8Bit-P/R.O.B.E.R.T/HardwareAndDesigns/Case/Arduino Mega 2560 _ RAMPS Holder with Quick Release - 2165053/images/20170305_114258__.jpg

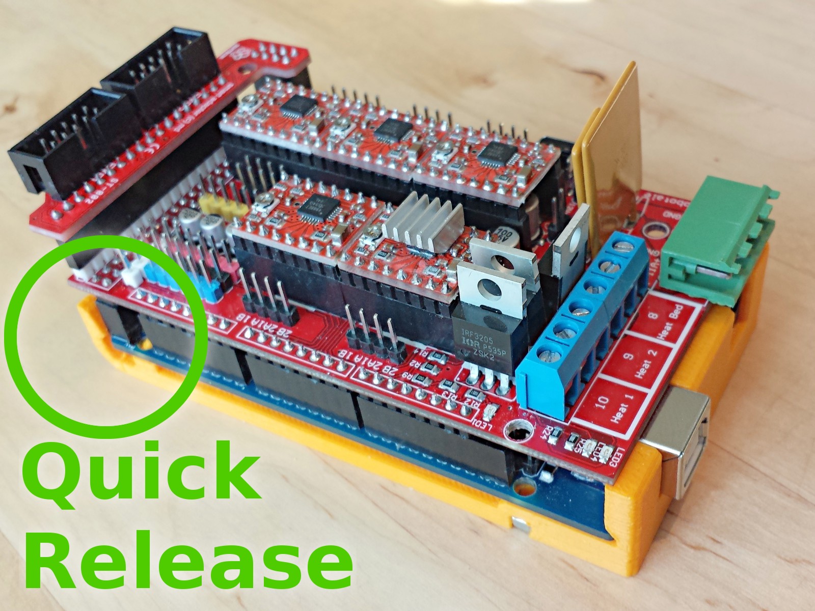
HardwareAndDesigns/Case/Arduino Mega 2560 _ RAMPS Holder with Quick Release - 2165053/images/20170305_114258__.jpg
