8Bit-P/R.O.B.E.R.T/HardwareAndDesigns/Robot Solidworks model/v.5/Motor 5 adapter.SLDPRT

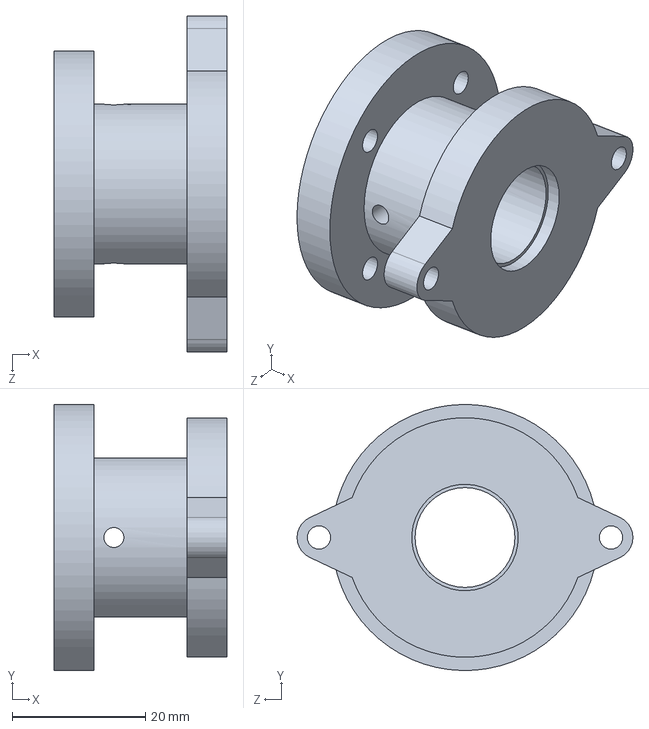
[picture p21: CAD file, 2024-06-12]
HardwareAndDesigns/Robot Solidworks model/v.5/Motor 5 adapter.SLDPRT
26.0 x 40.0 x 50.5 mm
