8Bit-P/R.O.B.E.R.T/HardwareAndDesigns/Stand/Baseplate.STL

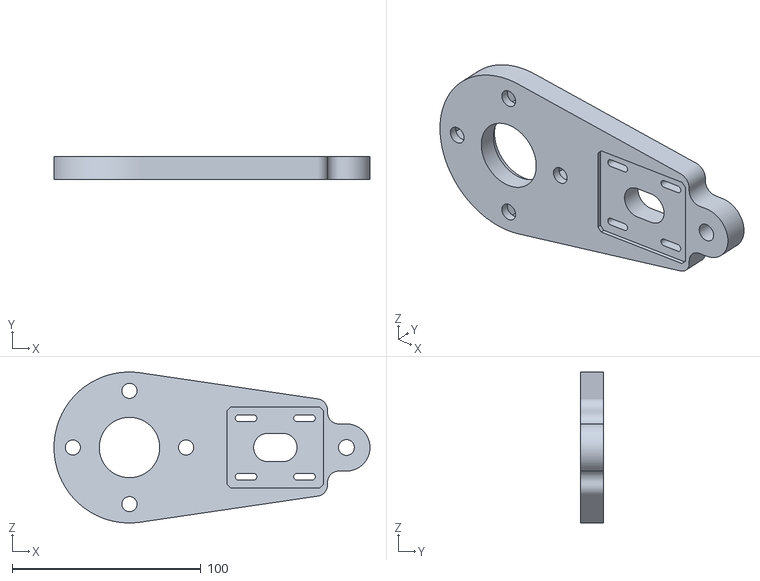
[picture p22: CAD file, 2024-06-12]
HardwareAndDesigns/Stand/Baseplate.STL
167.5 x 12.0 x 80.0
