8Bit-P/R.O.B.E.R.T/HardwareAndDesigns/Additional/LimitSwitchBase.stl

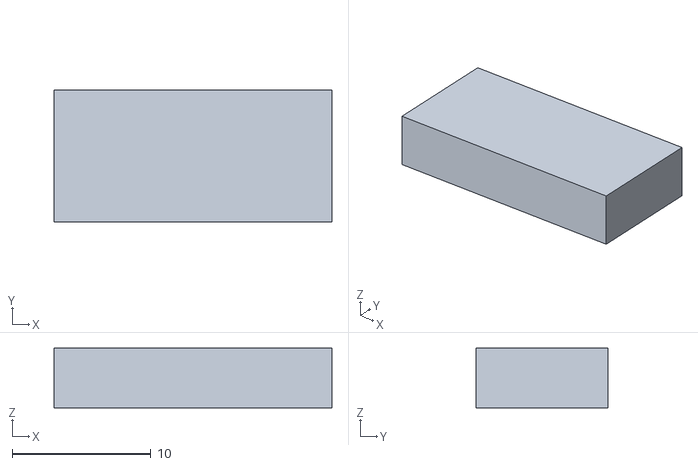
[picture p23: CAD file, 2024-12-18]
HardwareAndDesigns/Additional/LimitSwitchBase.stl
20.0 x 9.50 x 4.30
