8Bit-P/R.O.B.E.R.T/HardwareAndDesigns/Arm2/Rotation arm V3.STL

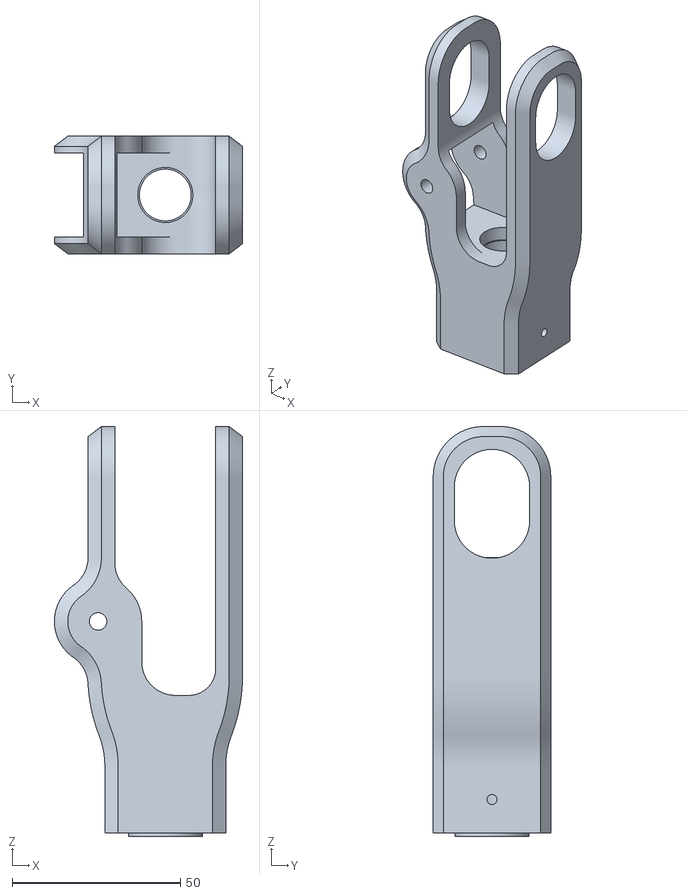
[picture p24: CAD file, 2024-06-12]
HardwareAndDesigns/Arm2/Rotation arm V3.STL
56.0 x 35.0 x 122.0
