8Bit-P/R.O.B.E.R.T/HardwareAndDesigns/Base/BaseWall_2_v2.STL

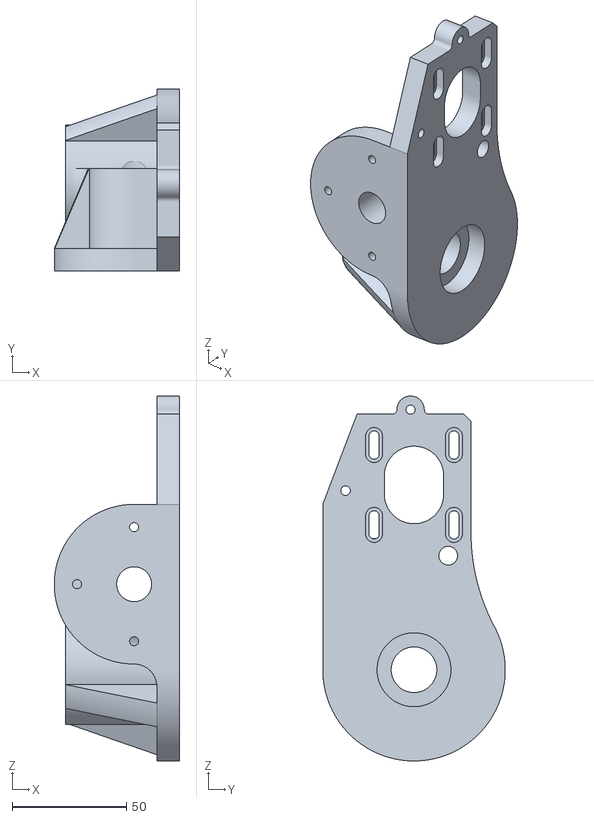
[picture p25: CAD file, 2024-06-12]
HardwareAndDesigns/Base/BaseWall_2_v2.STL
55.0 x 80.0 x 160.0
