8Bit-P/R.O.B.E.R.T/HardwareAndDesigns/Case/PowerSupplySupport.stl

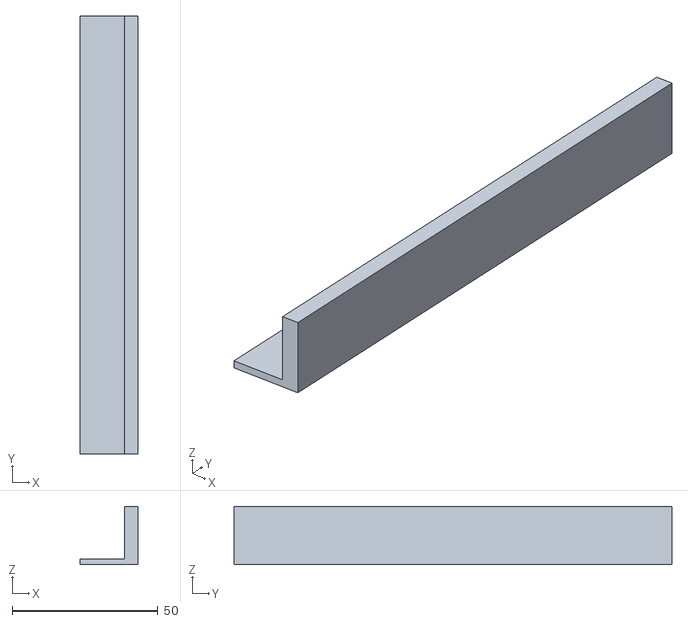
[picture p26: CAD file, 2025-02-12]
HardwareAndDesigns/Case/PowerSupplySupport.stl
20.0 x 150.0 x 20.0
