8Bit-P/R.O.B.E.R.T/HardwareAndDesigns/PiecesRework/ReductorSeparator.stl

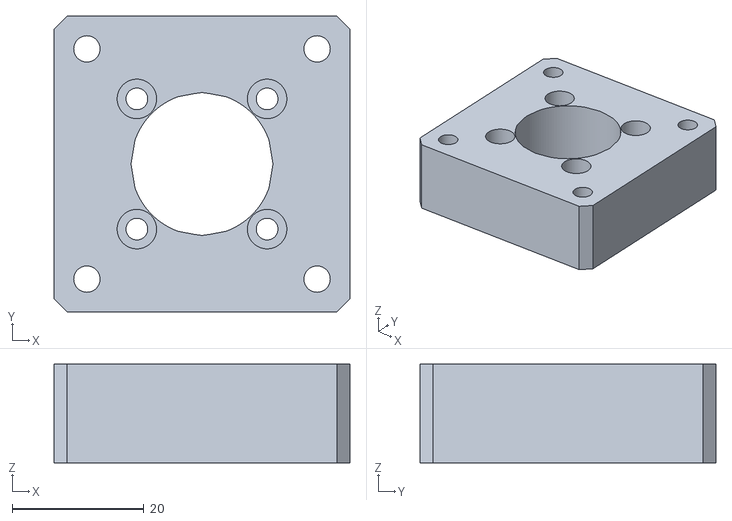
[picture p27: CAD file, 2024-12-13]
HardwareAndDesigns/PiecesRework/ReductorSeparator.stl
45.0 x 45.0 x 15.0
