8Bit-P/R.O.B.E.R.T/HardwareAndDesigns/Robot Solidworks model/Arm 4.3.SLDPRT

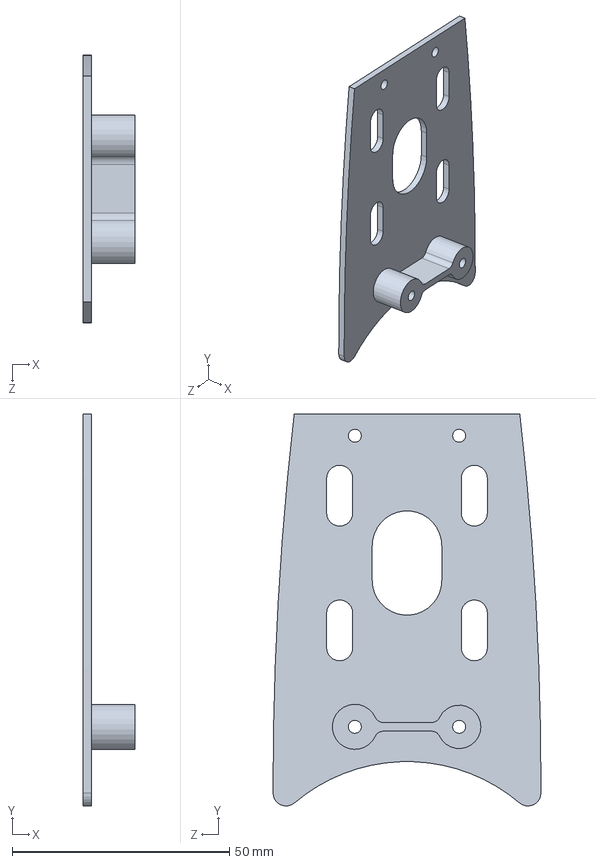
[picture p28: CAD file, 2024-06-12]
HardwareAndDesigns/Robot Solidworks model/Arm 4.3.SLDPRT
12.0 x 90.2 x 61.7 mm
