8Bit-P/R.O.B.E.R.T/HardwareAndDesigns/Robot Solidworks model/microswitch-ss-3gl13sl-1.snapshot.2/switch_lever.SLDPRT

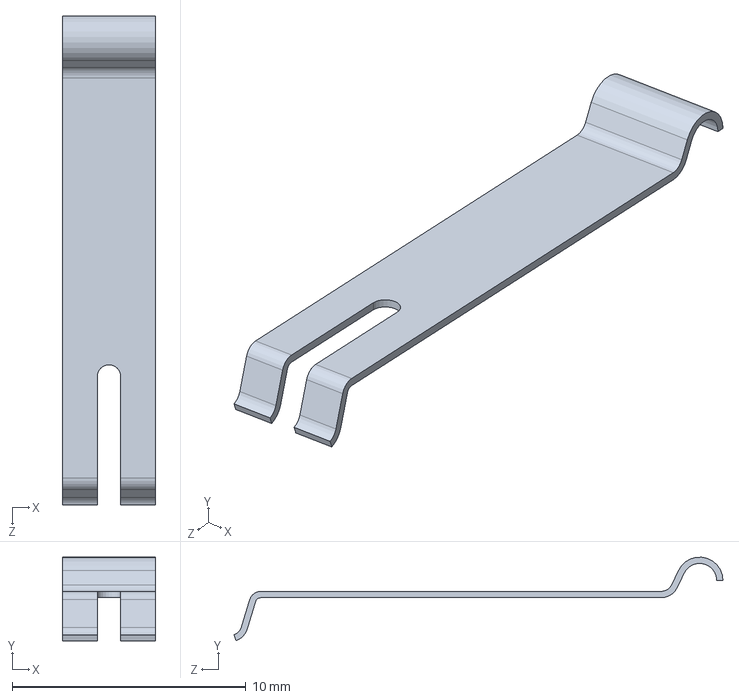
[picture p29: CAD file, 2024-06-12]
HardwareAndDesigns/Robot Solidworks model/microswitch-ss-3gl13sl-1.snapshot.2/switch_lever.SLDPRT
4.00 x 3.58 x 20.9 mm
