8Bit-P/R.O.B.E.R.T/HardwareAndDesigns/Robot Solidworks model/Solidworks/Nema 14 stepper.SLDPRT

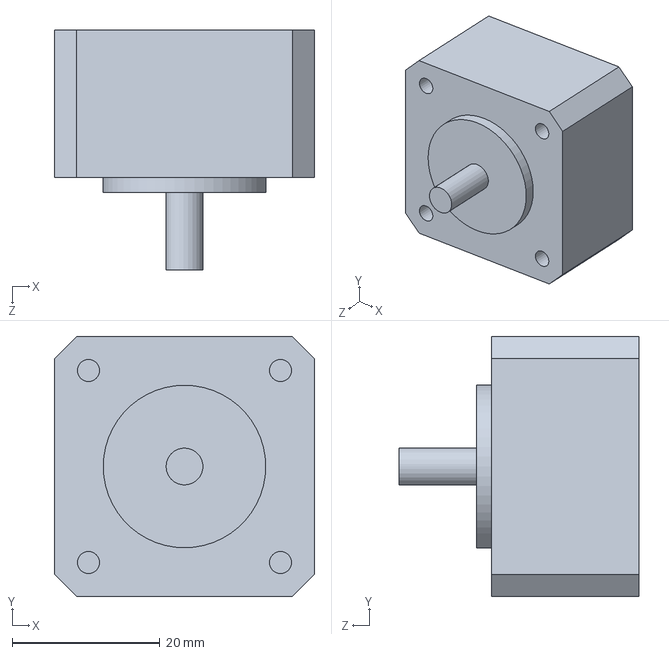
[picture p30: CAD file, 2024-06-12]
HardwareAndDesigns/Robot Solidworks model/Solidworks/Nema 14 stepper.SLDPRT
35.2 x 35.2 x 32.5 mm
