8Bit-P/R.O.B.E.R.T/HardwareAndDesigns/Robot Solidworks model/v.5/Pulley60Tv2.SLDPRT

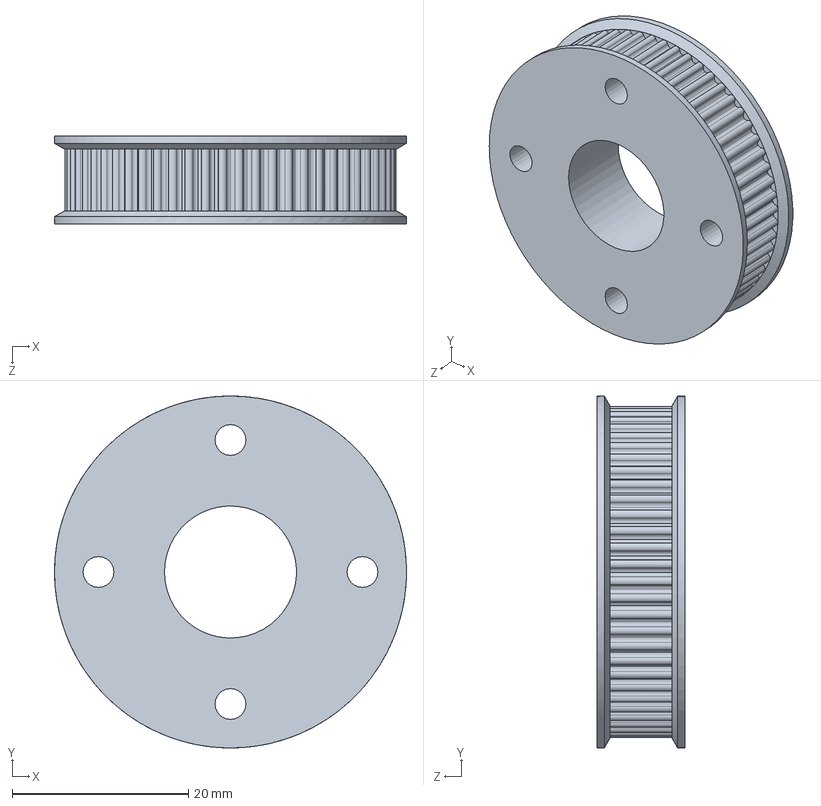
[picture p32: CAD file, 2024-06-12]
HardwareAndDesigns/Robot Solidworks model/v.5/Pulley60Tv2.SLDPRT
40.0 x 40.0 x 10.0 mm
