8Bit-P/R.O.B.E.R.T/HardwareAndDesigns/Stand/Bottom Tube.STL

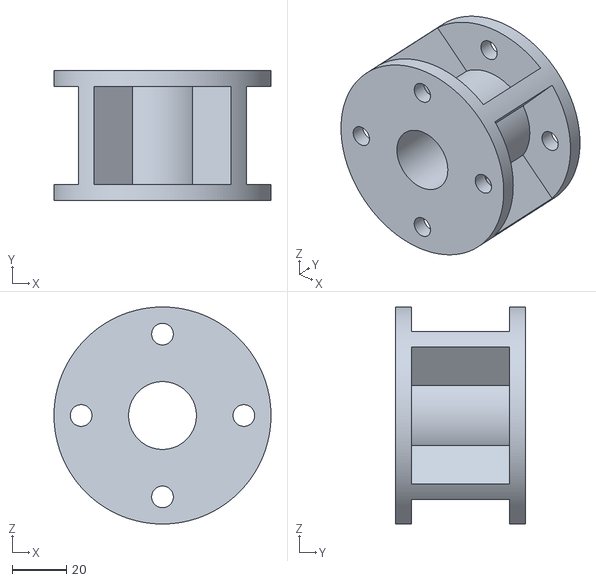
[picture p33: CAD file, 2024-06-12]
HardwareAndDesigns/Stand/Bottom Tube.STL
80.0 x 48.0 x 80.0
