8Bit-P/R.O.B.E.R.T/HardwareAndDesigns/Arm1/Arm1v2.STL

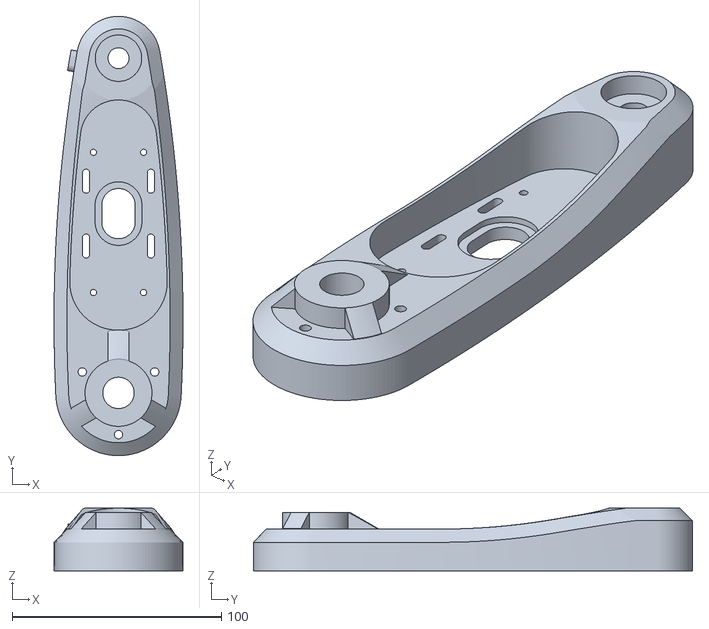
[picture p34: CAD file, 2024-06-12]
HardwareAndDesigns/Arm1/Arm1v2.STL
61.7 x 210.0 x 30.0
