8Bit-P/R.O.B.E.R.T/HardwareAndDesigns/Arm2/Pulley32TGT2.STL

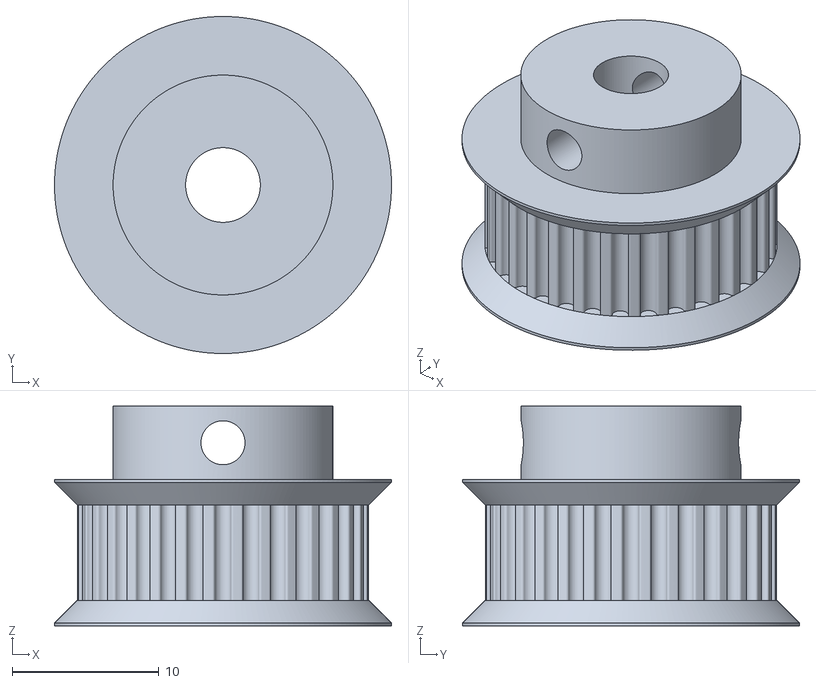
[picture p35: CAD file, 2024-06-12]
HardwareAndDesigns/Arm2/Pulley32TGT2.STL
23.0 x 23.0 x 15.0
