8Bit-P/R.O.B.E.R.T/HardwareAndDesigns/Base/Motor1 spacer.STL

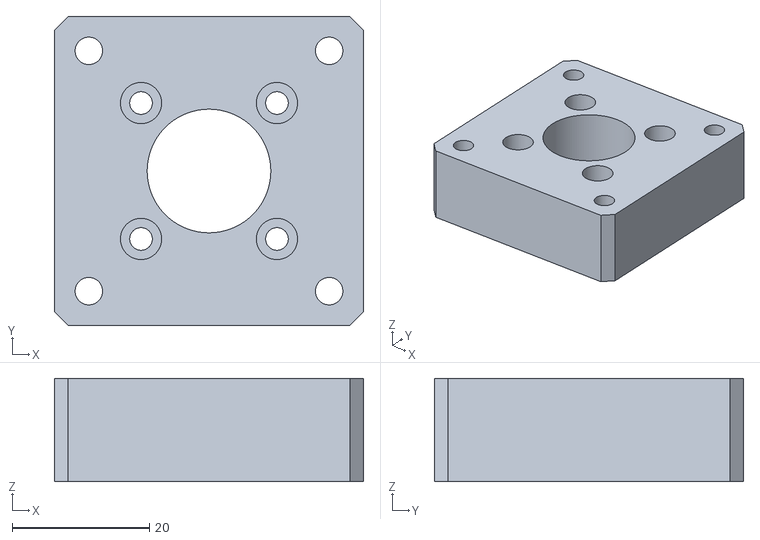
[picture p36: CAD file, 2024-06-12]
HardwareAndDesigns/Base/Motor1 spacer.STL
45.0 x 45.0 x 15.0
