8Bit-P/R.O.B.E.R.T/HardwareAndDesigns/Case/PowerSupplyHolder.stl

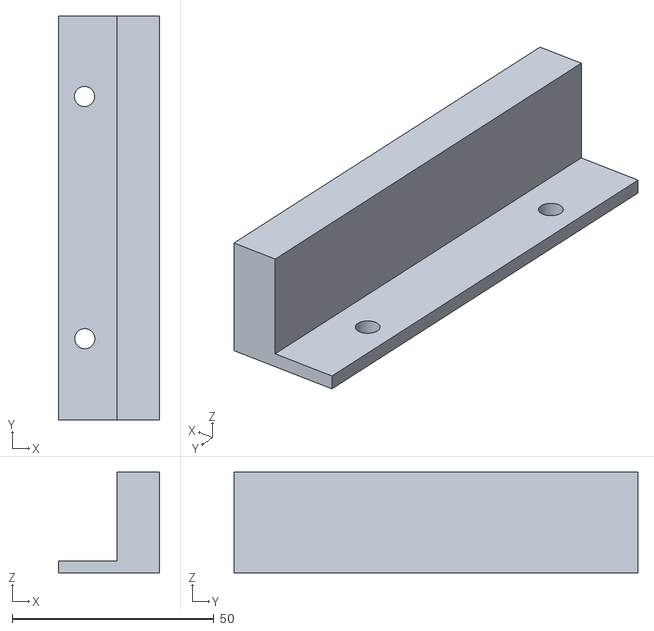
[picture p37: CAD file, 2025-02-12]
HardwareAndDesigns/Case/PowerSupplyHolder.stl
25.0 x 100.0 x 25.0
