8Bit-P/R.O.B.E.R.T/HardwareAndDesigns/Robot Solidworks model/ball bearings/thrust ball bearing_68_iso.sldprt

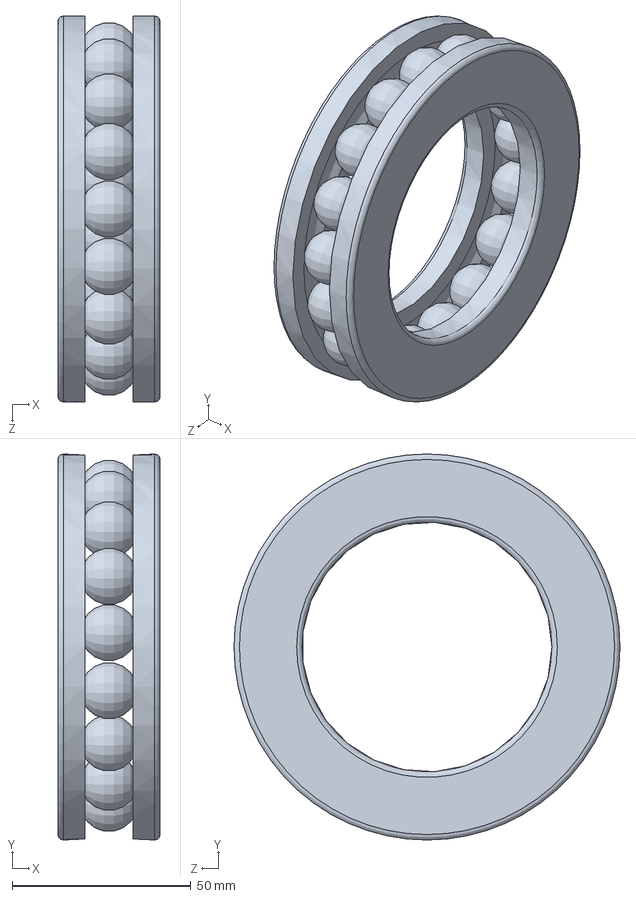
[picture p38: CAD file, 2024-06-12]
HardwareAndDesigns/Robot Solidworks model/ball bearings/thrust ball bearing_68_iso.sldprt
28.6 x 108.0 x 108.0 mm
