8Bit-P/R.O.B.E.R.T/HardwareAndDesigns/Robot Solidworks model/Solidworks/GT2_16T_13x14.SLDPRT

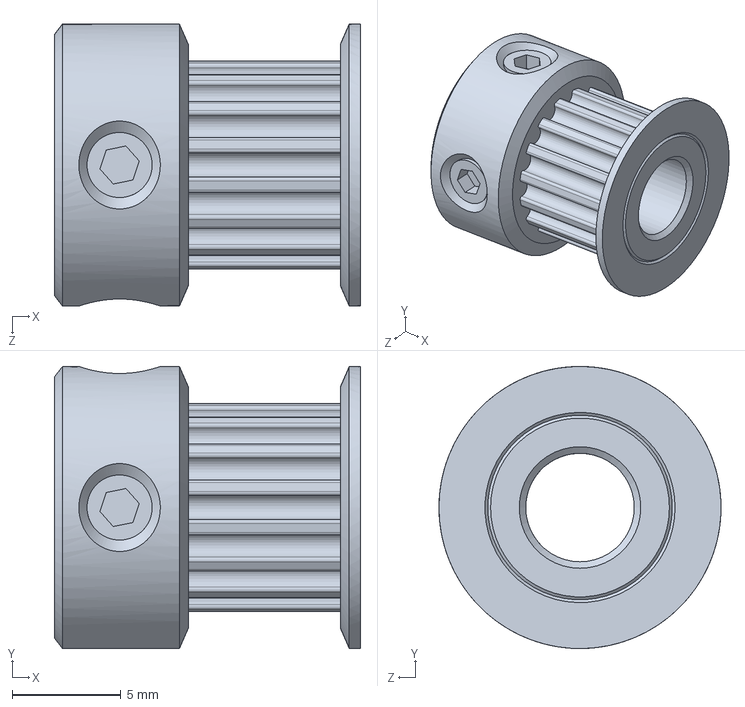
[picture p39: CAD file, 2024-06-12]
HardwareAndDesigns/Robot Solidworks model/Solidworks/GT2_16T_13x14.SLDPRT
14.1 x 13.0 x 13.0 mm
