8Bit-P/R.O.B.E.R.T/HardwareAndDesigns/Stand/Bottom support.STL

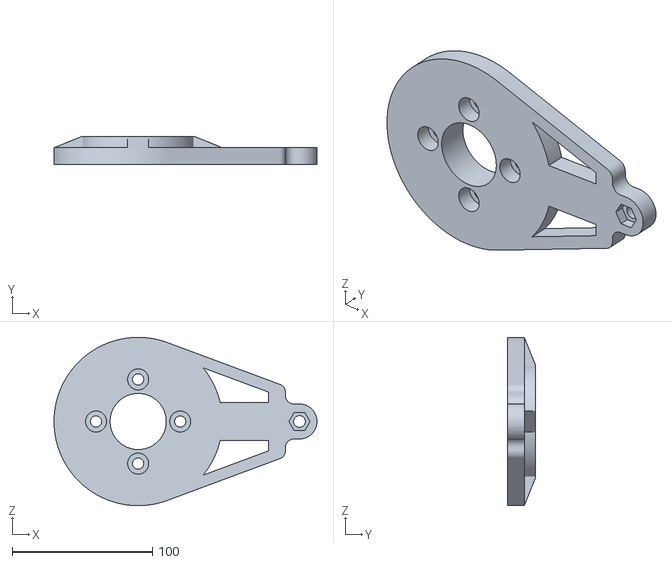
[picture p40: CAD file, 2024-06-12]
HardwareAndDesigns/Stand/Bottom support.STL
187.5 x 20.0 x 120.0
