8Bit-P/R.O.B.E.R.T/HardwareAndDesigns/Arm1/HTD80T 2mm spacer.STL

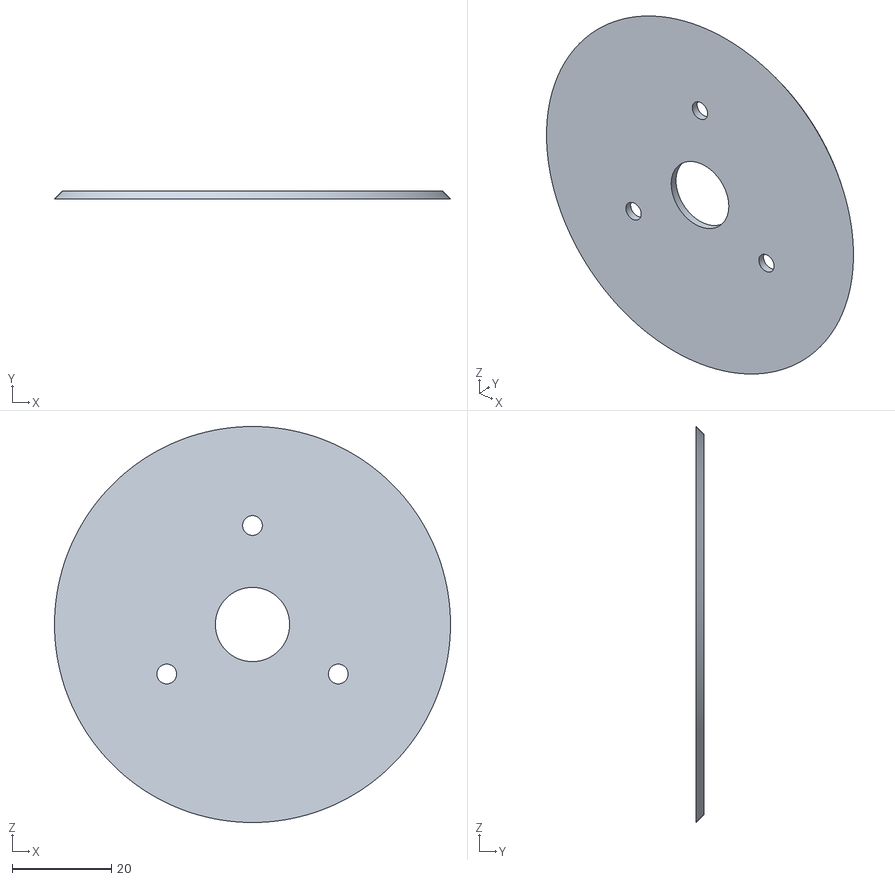
[picture p41: CAD file, 2024-06-12]
HardwareAndDesigns/Arm1/HTD80T 2mm spacer.STL
80.0 x 1.60 x 80.0
