8Bit-P/R.O.B.E.R.T/HardwareAndDesigns/Arm2/Arm2Mountv2.STL

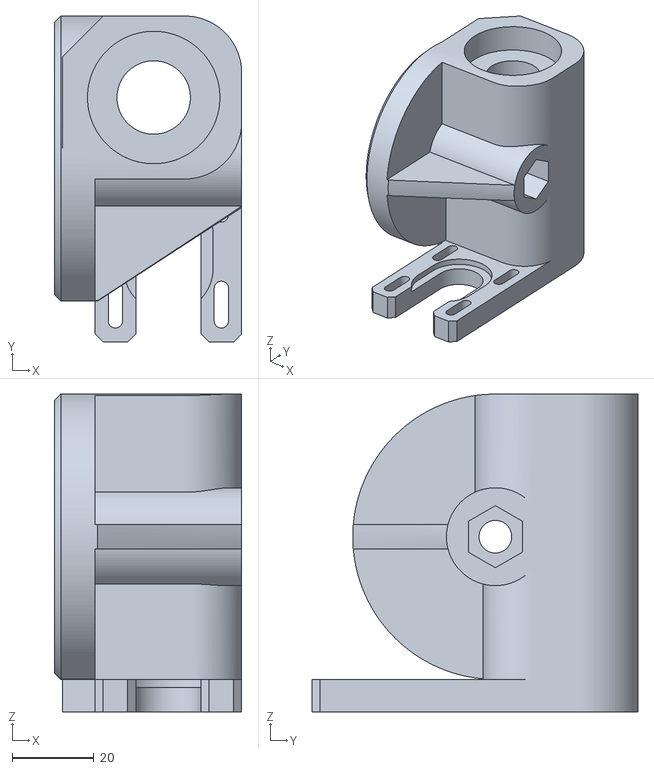
[picture p42: CAD file, 2024-06-12]
HardwareAndDesigns/Arm2/Arm2Mountv2.STL
46.0 x 80.0 x 78.0
