8Bit-P/R.O.B.E.R.T/HardwareAndDesigns/Base/Basewall cover v2.STL

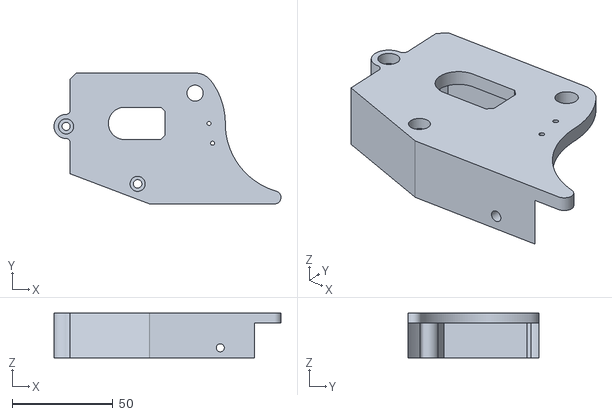
[picture p43: CAD file, 2024-06-12]
HardwareAndDesigns/Base/Basewall cover v2.STL
112.6 x 65.0 x 22.2
