8Bit-P/R.O.B.E.R.T/HardwareAndDesigns/Case/BottomPlate2.stl

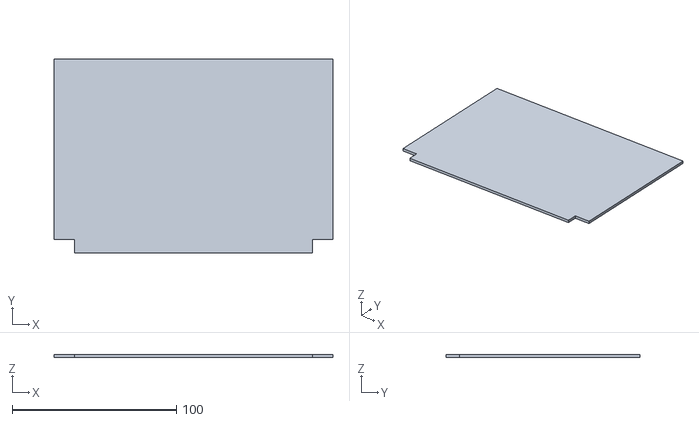
[picture p44: CAD file, 2025-02-12]
HardwareAndDesigns/Case/BottomPlate2.stl
170.0 x 118.0 x 2.00
