8Bit-P/R.O.B.E.R.T/HardwareAndDesigns/Robot Solidworks model/microswitch-ss-3gl13sl-1.snapshot.2/limit-switch-top-case.SLDPRT

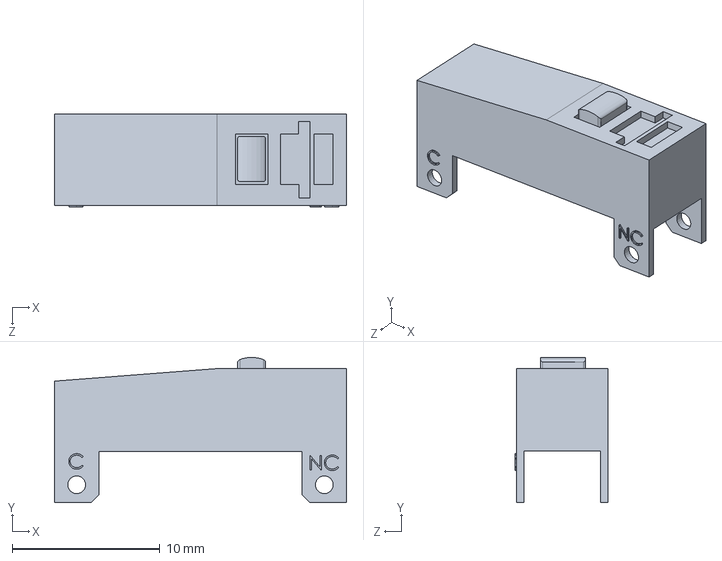
[picture p45: CAD file, 2024-06-12]
HardwareAndDesigns/Robot Solidworks model/microswitch-ss-3gl13sl-1.snapshot.2/limit-switch-top-case.SLDPRT
19.8 x 9.81 x 6.30 mm
