8Bit-P/R.O.B.E.R.T/HardwareAndDesigns/Robot Solidworks model/Solidworks/Nema 14 Round stepper.SLDPRT

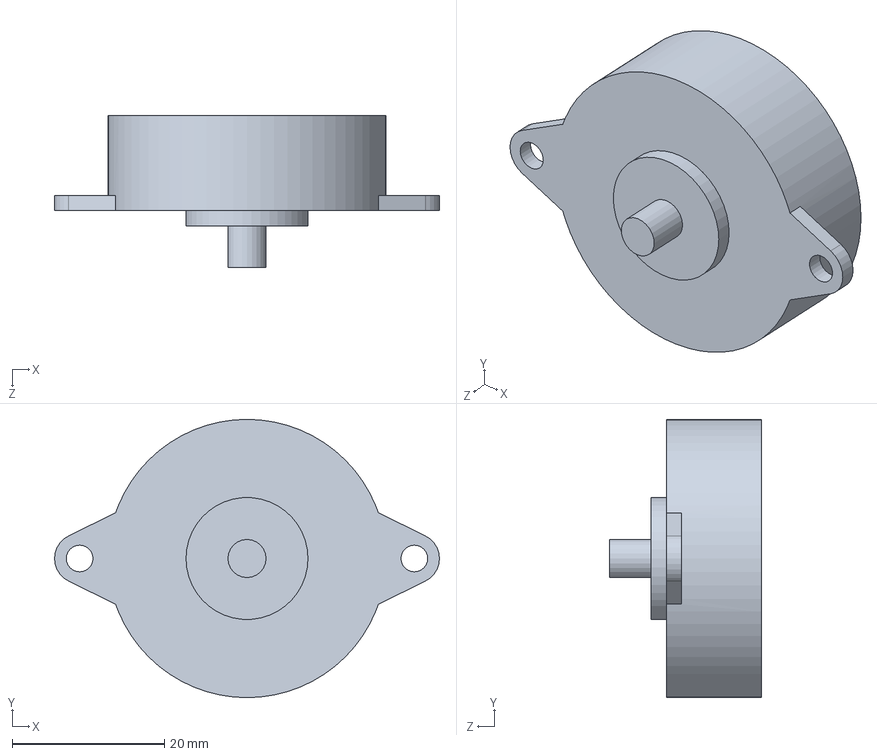
[picture p46: CAD file, 2024-06-12]
HardwareAndDesigns/Robot Solidworks model/Solidworks/Nema 14 Round stepper.SLDPRT
50.5 x 36.5 x 20.0 mm
