8Bit-P/R.O.B.E.R.T/HardwareAndDesigns/Robot Solidworks model/stepper-motor-nema-17.snapshot.17/Base.SLDPRT

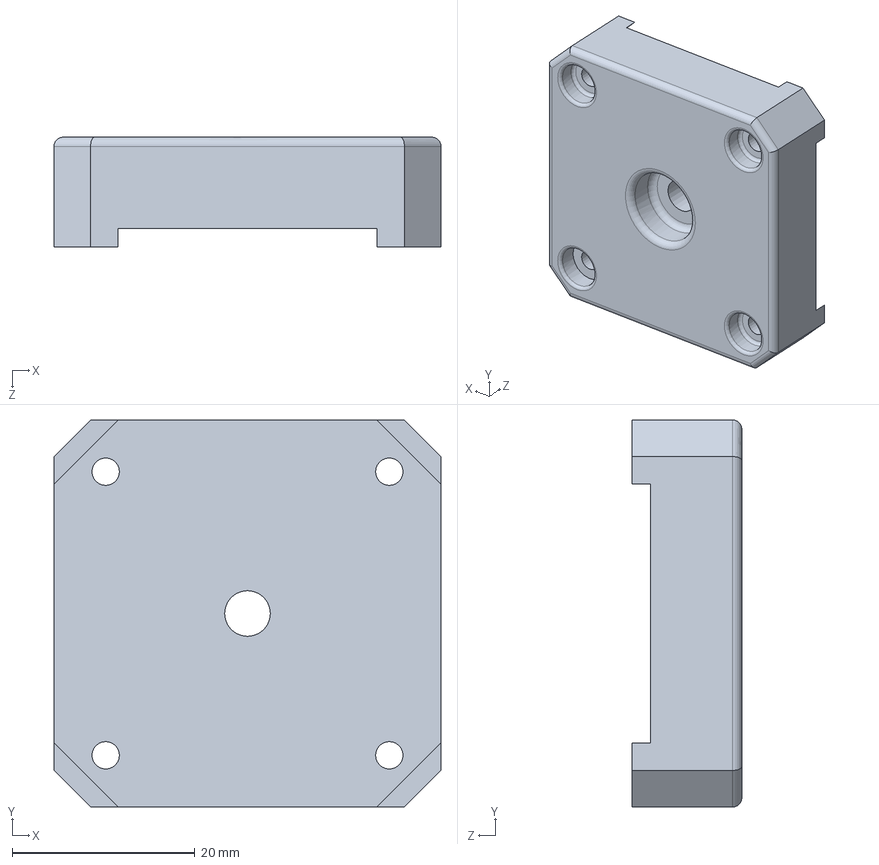
[picture p47: CAD file, 2024-06-12]
HardwareAndDesigns/Robot Solidworks model/stepper-motor-nema-17.snapshot.17/Base.SLDPRT
42.3 x 42.3 x 12.0 mm
