8Bit-P/R.O.B.E.R.T/HardwareAndDesigns/Case/Base Top Half.stl

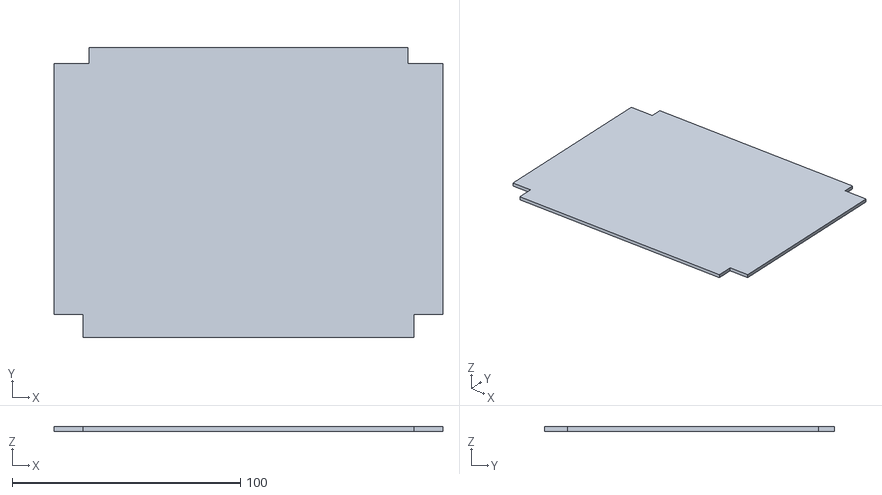
[picture p48: CAD file, 2025-02-12]
HardwareAndDesigns/Case/Base Top Half.stl
170.5 x 127.0 x 2.00
