8Bit-P/R.O.B.E.R.T/HardwareAndDesigns/Robot Solidworks model/microswitch-ss-3gl13sl-1.snapshot.2/pins.SLDPRT

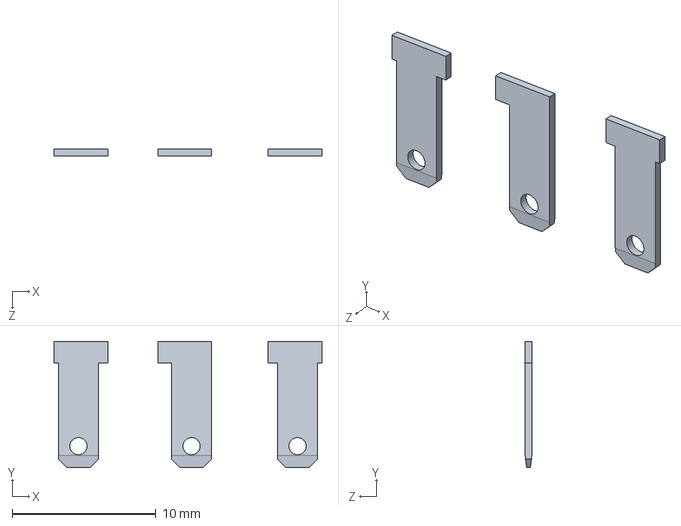
[picture p49: CAD file, 2024-06-12]
HardwareAndDesigns/Robot Solidworks model/microswitch-ss-3gl13sl-1.snapshot.2/pins.SLDPRT
18.6 x 8.80 x 0.47 mm
