8Bit-P/R.O.B.E.R.T/HardwareAndDesigns/Robot Solidworks model/stepper-motor-nema-17.snapshot.17/Eje.SLDPRT

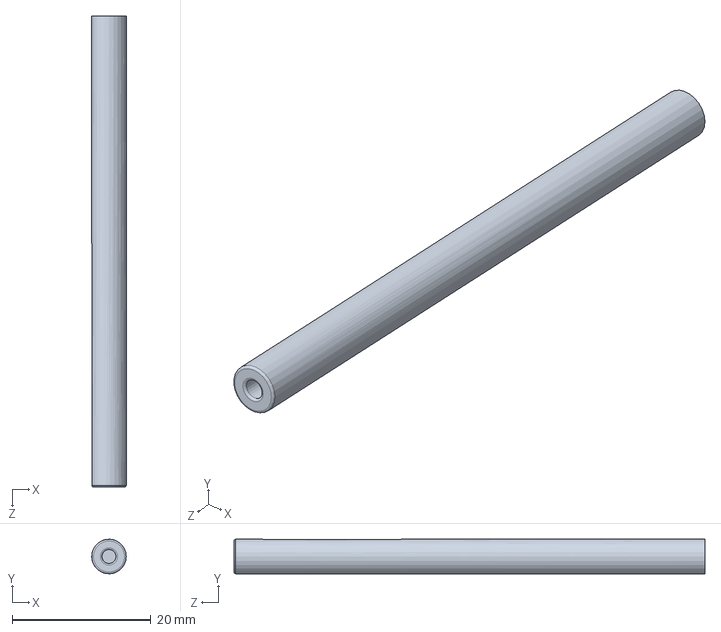
[picture p50: CAD file, 2024-06-12]
HardwareAndDesigns/Robot Solidworks model/stepper-motor-nema-17.snapshot.17/Eje.SLDPRT
5.00 x 5.00 x 68.0 mm
