8Bit-P/R.O.B.E.R.T/HardwareAndDesigns/Case/ConnectorPannel v5.stl

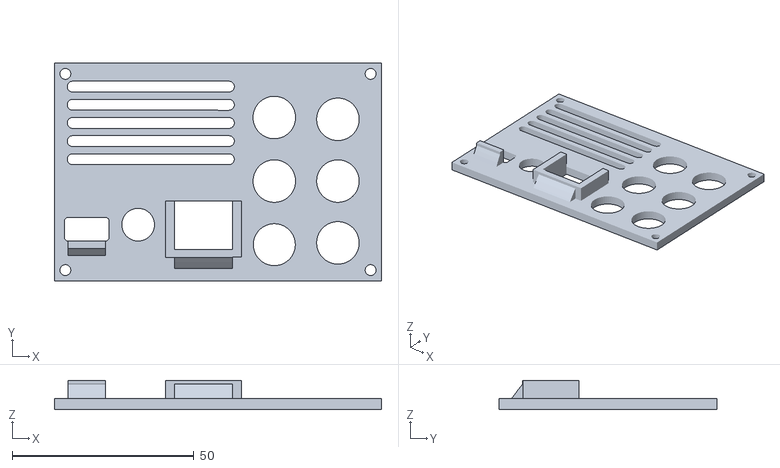
[picture p51: CAD file, 2025-02-12]
HardwareAndDesigns/Case/ConnectorPannel v5.stl
90.0 x 60.0 x 8.00
