8Bit-P/R.O.B.E.R.T/HardwareAndDesigns/Robot Solidworks model/3M HTD 16T 6mm Bore.SLDPRT

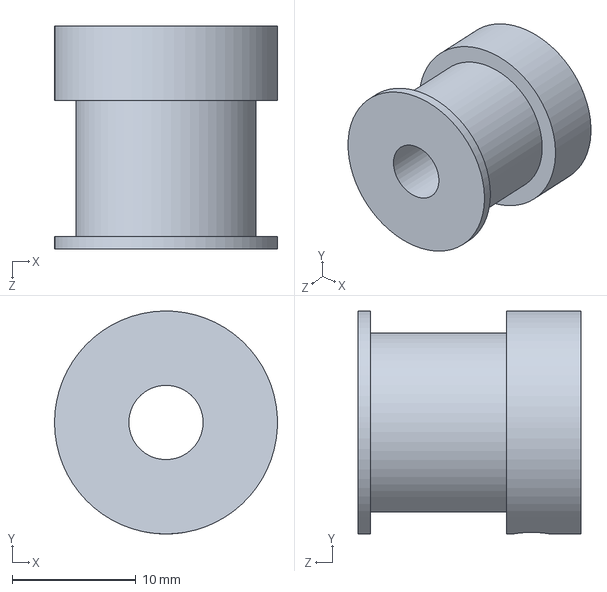
[picture p52: CAD file, 2024-06-12]
HardwareAndDesigns/Robot Solidworks model/3M HTD 16T 6mm Bore.SLDPRT
18.0 x 18.0 x 18.0 mm
