8Bit-P/R.O.B.E.R.T/HardwareAndDesigns/Arm2/GT2 belt chamfer roller.STL

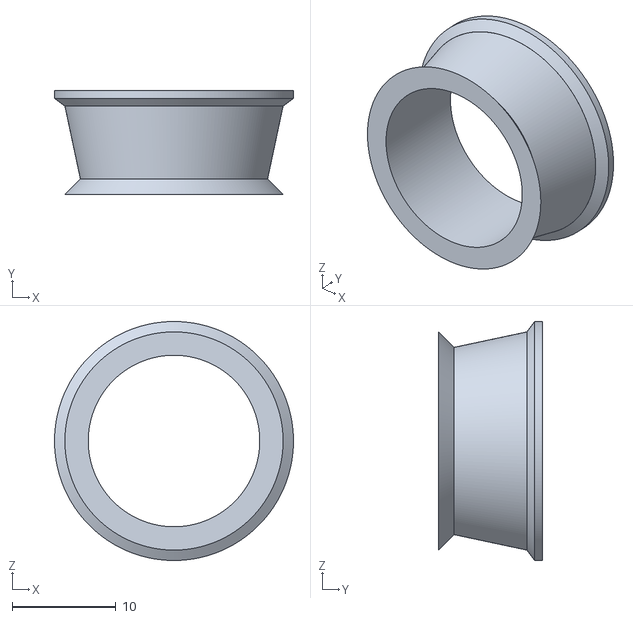
[picture p53: CAD file, 2024-06-12]
HardwareAndDesigns/Arm2/GT2 belt chamfer roller.STL
23.0 x 10.0 x 23.0
