8Bit-P/R.O.B.E.R.T/HardwareAndDesigns/Case/USBc v1.stl

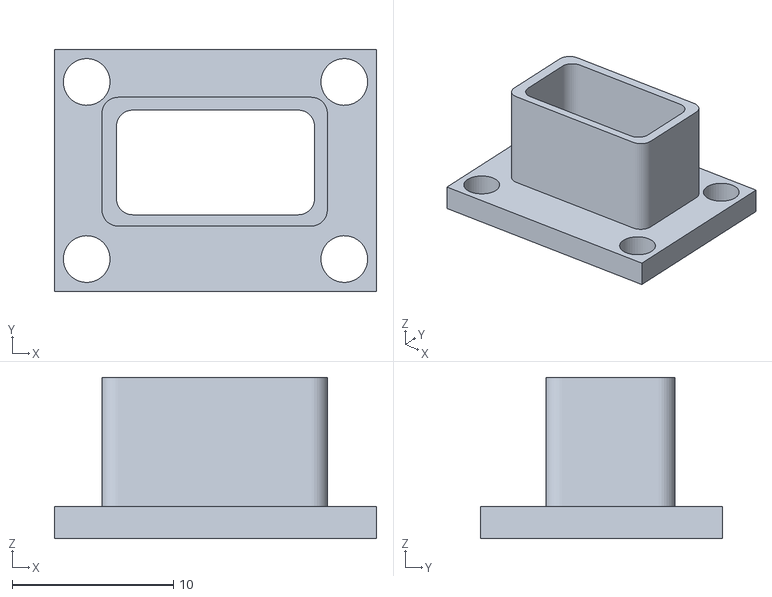
[picture p54: CAD file, 2025-02-12]
HardwareAndDesigns/Case/USBc v1.stl
20.0 x 15.0 x 10.0
