8Bit-P/R.O.B.E.R.T/HardwareAndDesigns/Robot Solidworks model/Pulley100Tv5.SLDPRT

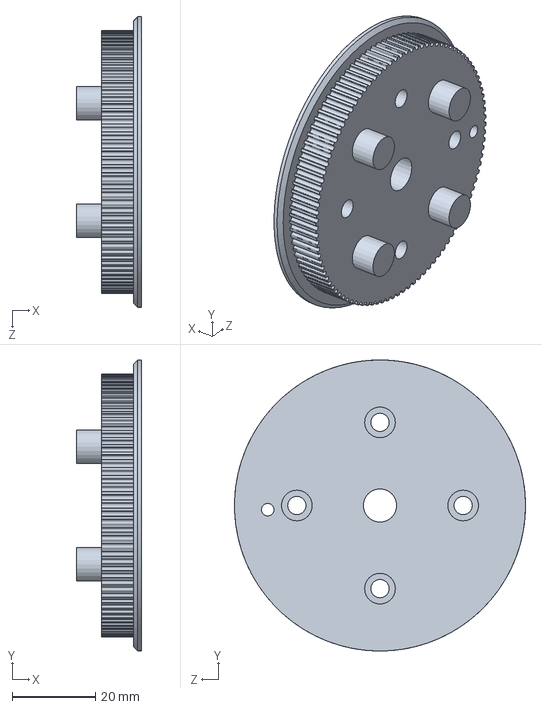
[picture p55: CAD file, 2024-06-12]
HardwareAndDesigns/Robot Solidworks model/Pulley100Tv5.SLDPRT
15.6 x 70.0 x 70.0 mm
