8Bit-P/R.O.B.E.R.T/HardwareAndDesigns/Arm2/J6 housing.STL

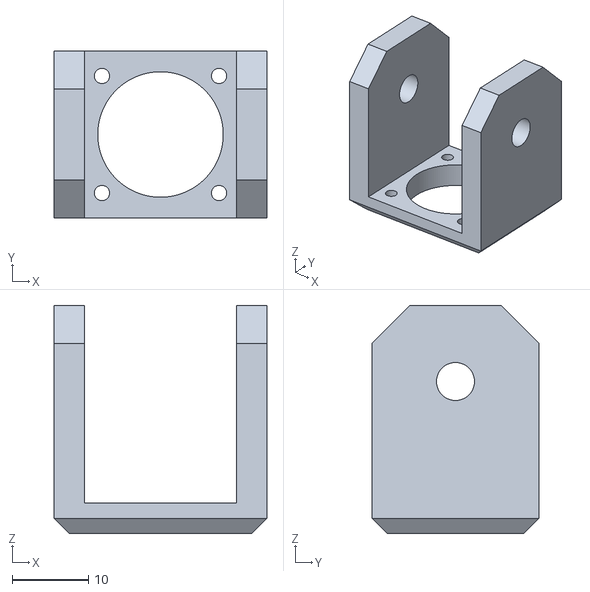
[picture p56: CAD file, 2024-06-12]
HardwareAndDesigns/Arm2/J6 housing.STL
28.0 x 22.0 x 30.0
