8Bit-P/R.O.B.E.R.T/HardwareAndDesigns/Case/ConnectorPannel.stl

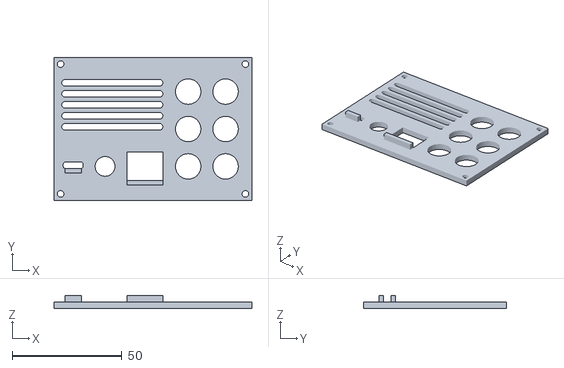
[picture p57: CAD file, 2025-02-12]
HardwareAndDesigns/Case/ConnectorPannel.stl
90.0 x 65.0 x 6.00
