8Bit-P/R.O.B.E.R.T/HardwareAndDesigns/Case/Box.stl

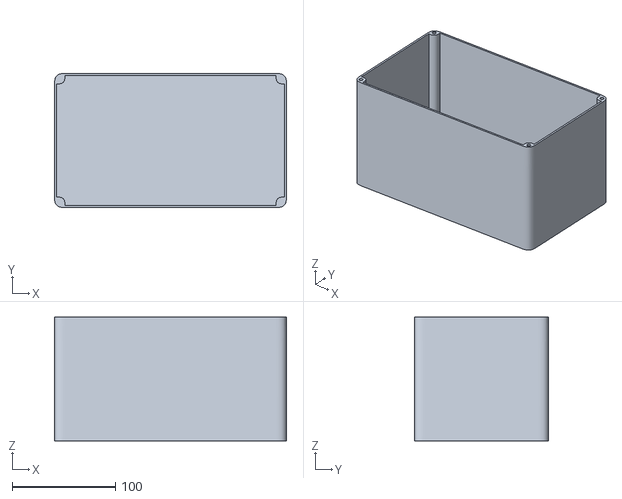
[picture p58: CAD file, 2024-12-18]
HardwareAndDesigns/Case/Box.stl
225.0 x 130.0 x 120.0
