8Bit-P/R.O.B.E.R.T/HardwareAndDesigns/Case/Electronics Box 180mmx130mmx60mm.SLDPRT

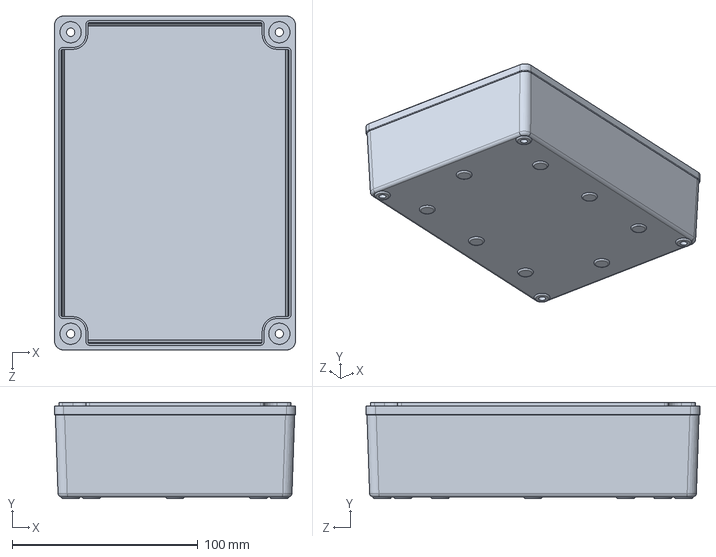
[picture p59: CAD file, 2024-12-13]
HardwareAndDesigns/Case/Electronics Box 180mmx130mmx60mm.SLDPRT
130.0 x 52.0 x 180.0 mm
