8Bit-P/R.O.B.E.R.T/HardwareAndDesigns/Robot Solidworks model/100mm aluputki.SLDPRT

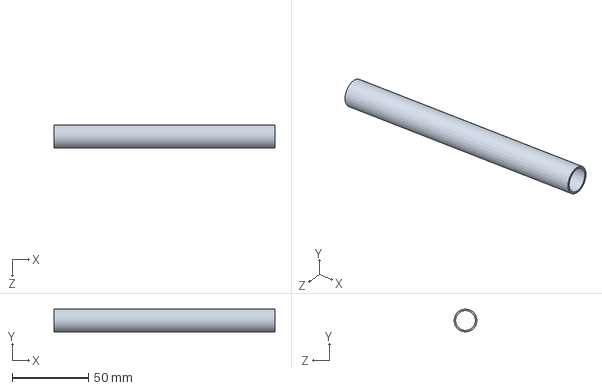
[picture p60: CAD file, 2024-06-12]
HardwareAndDesigns/Robot Solidworks model/100mm aluputki.SLDPRT
145.0 x 15.0 x 15.0 mm
