8Bit-P/R.O.B.E.R.T/HardwareAndDesigns/Robot Solidworks model/6mm akseli.SLDPRT

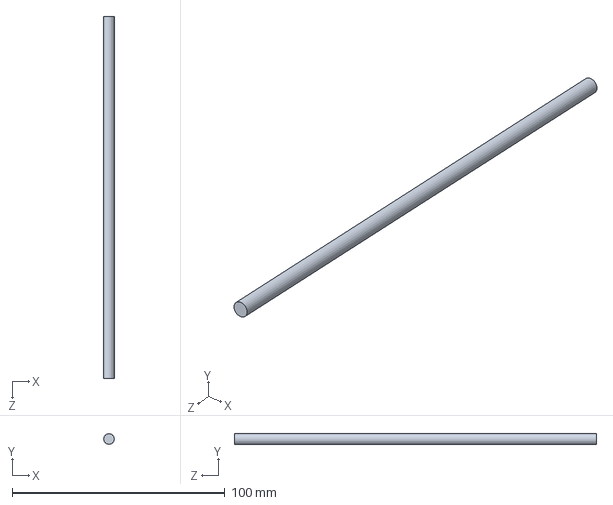
[picture p61: CAD file, 2024-06-12]
HardwareAndDesigns/Robot Solidworks model/6mm akseli.SLDPRT
5.00 x 5.00 x 170.0 mm
