8Bit-P/R.O.B.E.R.T/HardwareAndDesigns/Robot Solidworks model/Nema8 Stepperi (banggood.com).SLDPRT

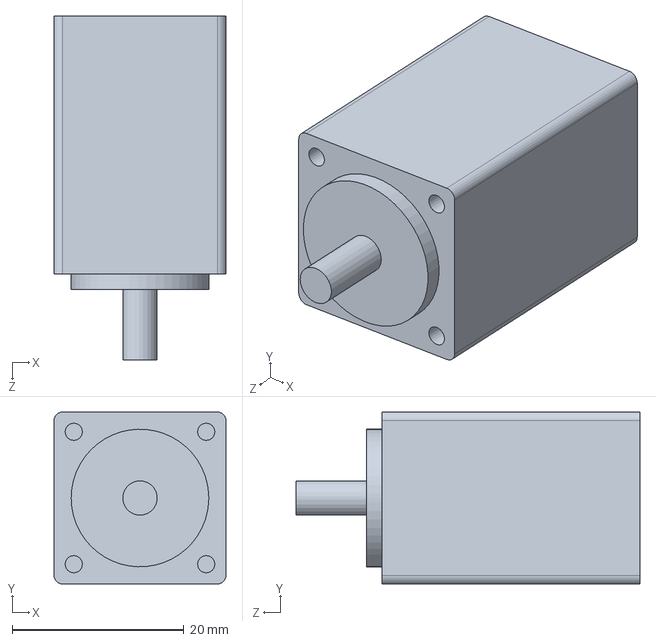
[picture p62: CAD file, 2024-06-12]
HardwareAndDesigns/Robot Solidworks model/Nema8 Stepperi (banggood.com).SLDPRT
20.0 x 20.0 x 40.0 mm
