8Bit-P/R.O.B.E.R.T/HardwareAndDesigns/Robot Solidworks model/Nema 17 planetary 5 to 1 gearbox.SLDPRT

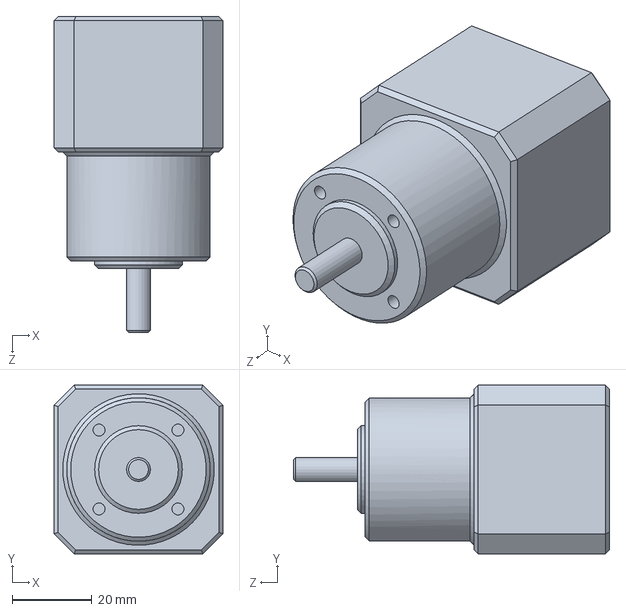
[picture p63: CAD file, 2024-06-12]
HardwareAndDesigns/Robot Solidworks model/Nema 17 planetary 5 to 1 gearbox.SLDPRT
42.3 x 42.3 x 79.3 mm
