8Bit-P/R.O.B.E.R.T/HardwareAndDesigns/Robot Solidworks model/15mm rikka 1.2mm.SLDPRT

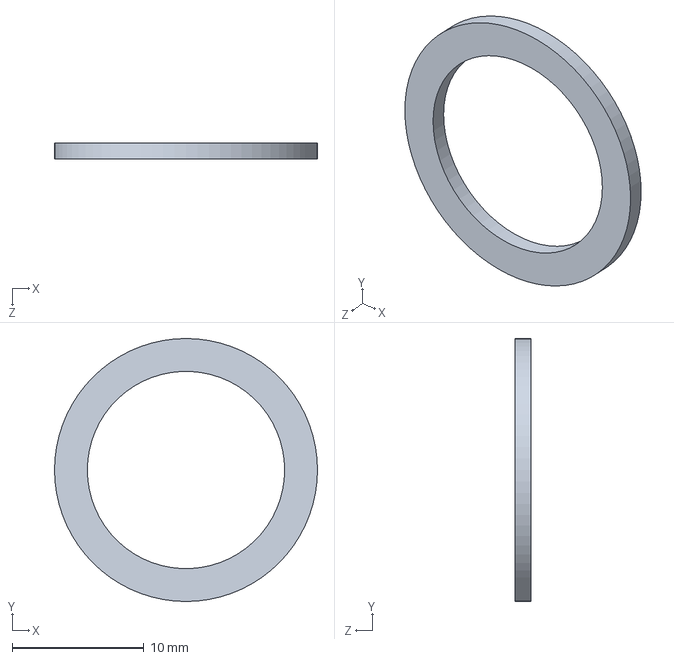
[picture p64: CAD file, 2024-06-12]
HardwareAndDesigns/Robot Solidworks model/15mm rikka 1.2mm.SLDPRT
20.0 x 20.0 x 1.20 mm
