8Bit-P/R.O.B.E.R.T/HardwareAndDesigns/Robot Solidworks model/15mm 1.6 rikka.SLDPRT

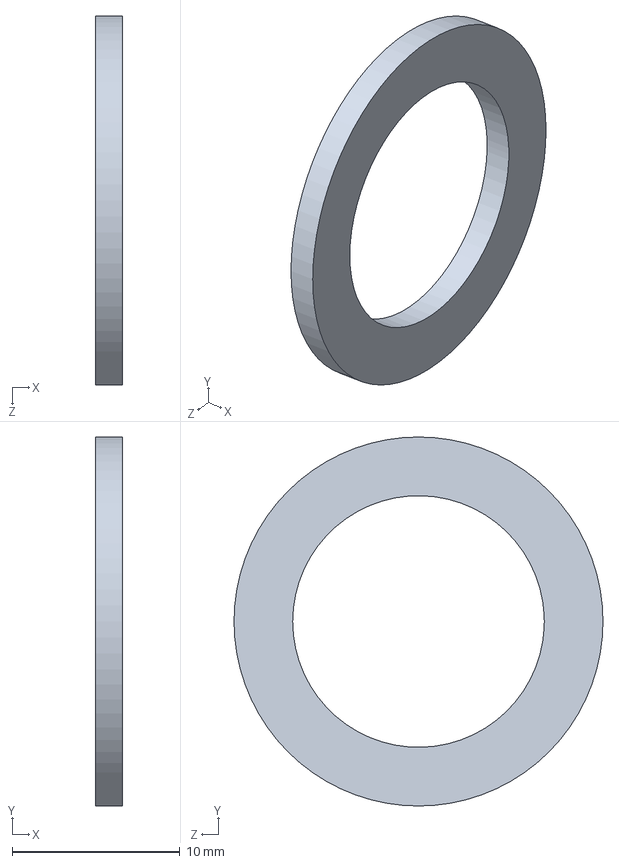
[picture p65: CAD file, 2024-06-12]
HardwareAndDesigns/Robot Solidworks model/15mm 1.6 rikka.SLDPRT
1.60 x 22.0 x 22.0 mm
