8Bit-P/R.O.B.E.R.T/HardwareAndDesigns/Robot Solidworks model/5mm akseli 1.SLDPRT

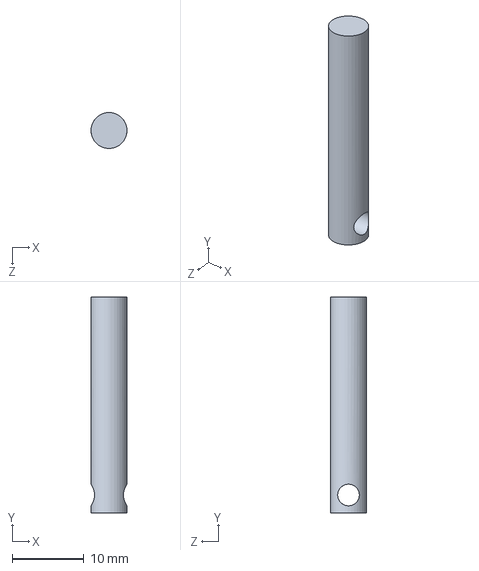
[picture p66: CAD file, 2024-06-12]
HardwareAndDesigns/Robot Solidworks model/5mm akseli 1.SLDPRT
5.00 x 30.0 x 5.00 mm
