8Bit-P/R.O.B.E.R.T/HardwareAndDesigns/Robot Solidworks model/5mm akseli 2.SLDPRT

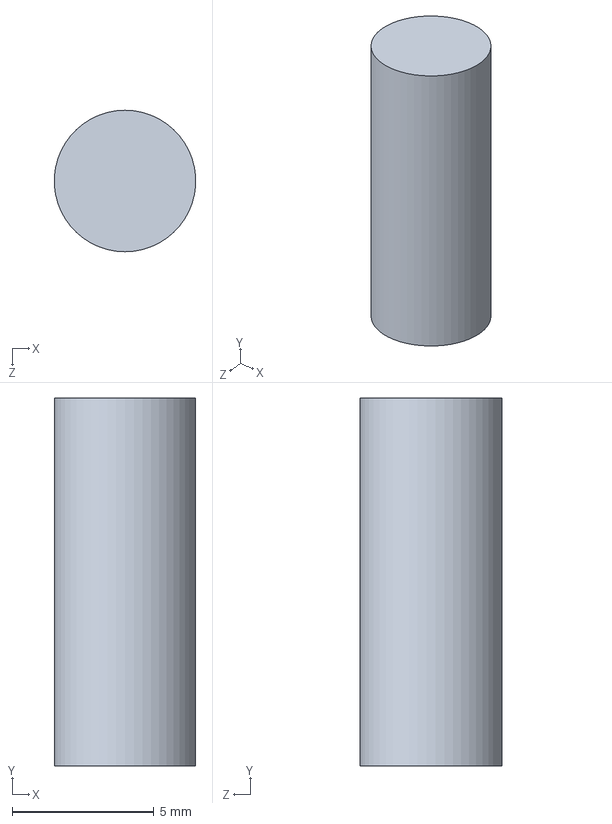
[picture p67: CAD file, 2024-06-12]
HardwareAndDesigns/Robot Solidworks model/5mm akseli 2.SLDPRT
4.99 x 13.0 x 5.00 mm
