8Bit-P/R.O.B.E.R.T/HardwareAndDesigns/Robot Solidworks model/Bottom spacer.SLDPRT

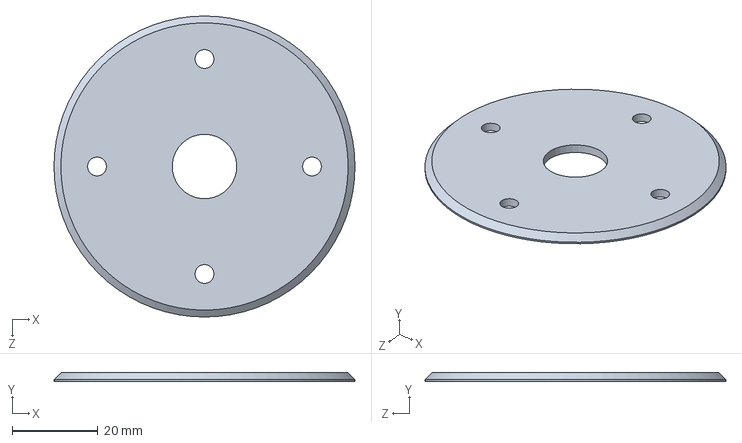
[picture p68: CAD file, 2024-06-12]
HardwareAndDesigns/Robot Solidworks model/Bottom spacer.SLDPRT
70.0 x 2.00 x 70.0 mm
