8Bit-P/R.O.B.E.R.T/HardwareAndDesigns/Robot Solidworks model/90mm aluputki.SLDPRT

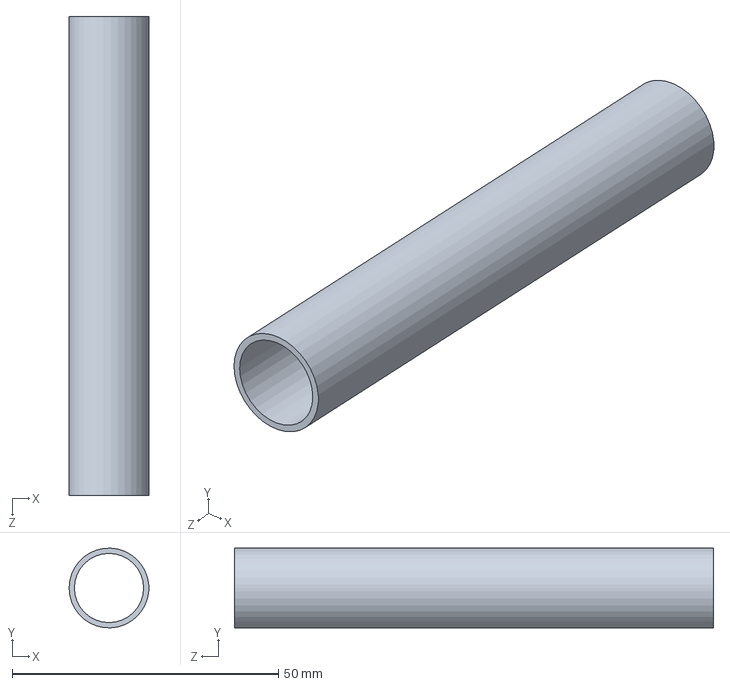
[picture p69: CAD file, 2024-06-12]
HardwareAndDesigns/Robot Solidworks model/90mm aluputki.SLDPRT
15.0 x 15.0 x 90.0 mm
