8Bit-P/R.O.B.E.R.T/HardwareAndDesigns/Robot Solidworks model/HTD pulley adapter.SLDPRT

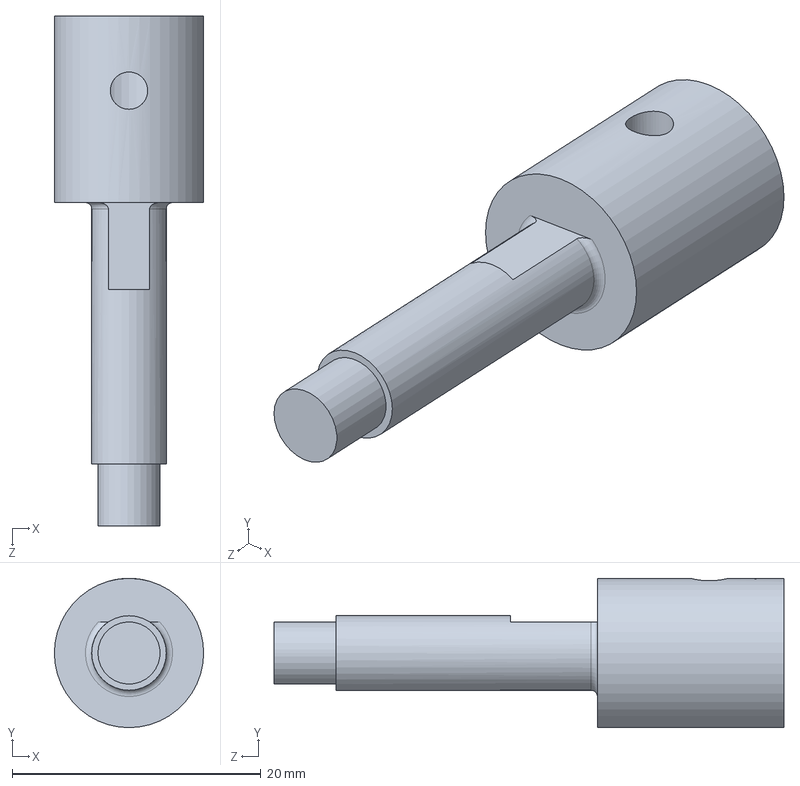
[picture p70: CAD file, 2024-06-12]
HardwareAndDesigns/Robot Solidworks model/HTD pulley adapter.SLDPRT
12.0 x 12.0 x 41.0 mm
