8Bit-P/R.O.B.E.R.T/HardwareAndDesigns/Robot Solidworks model/Toothless pulley 16t gt2.SLDPRT

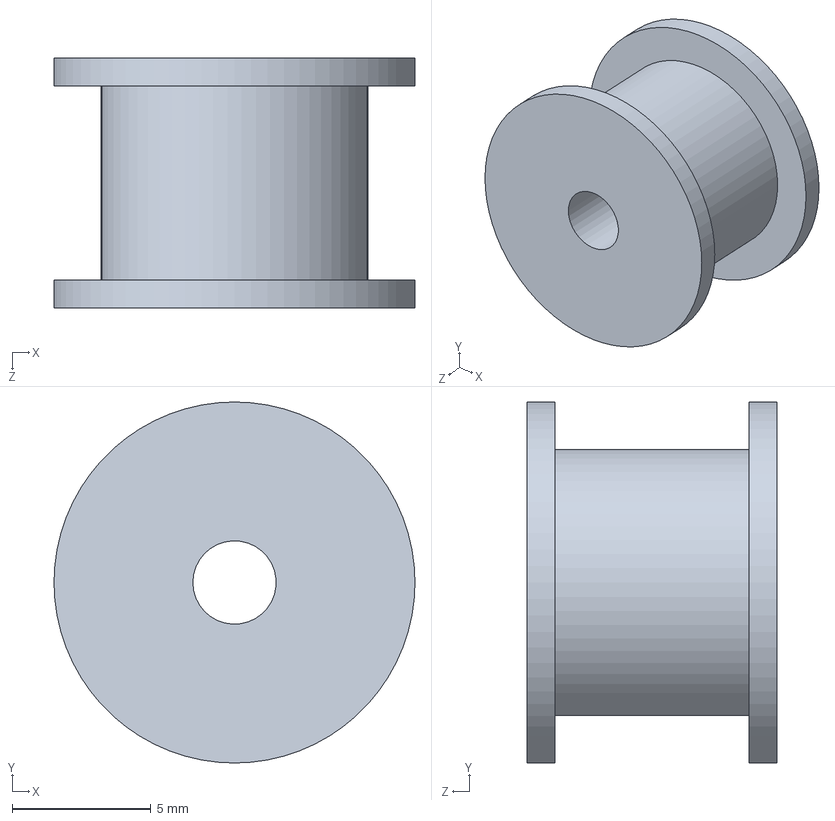
[picture p71: CAD file, 2024-06-12]
HardwareAndDesigns/Robot Solidworks model/Toothless pulley 16t gt2.SLDPRT
13.0 x 13.0 x 9.00 mm
