8Bit-P/R.O.B.E.R.T/ArduinoScripts/SerialController/SerialController.ino

#include "StepperManager.h"
#include "CommandProcessor.h"
#include "Constants.h"

void setup() {
  Serial.begin(115200);
  // Set the maximum speed in steps per second:
  initializeSteppers();
}

void loop() {
  while(Serial.available()) {
    String command = Serial.readStringUntil('~');
    processCommand(command);
  }
}
